sorchowski/odometry/schematics/DualEncoderI2C/dual-encoder-i2c-board-revf.png

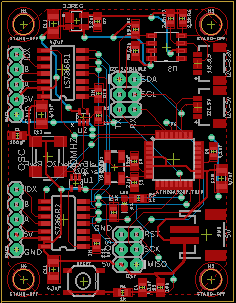
schematics/DualEncoderI2C/dual-encoder-i2c-board-revf.png
