sorchowski/odometry/schematics/DualEncoderShield3v/dual-encoder-shield-3v.jpg

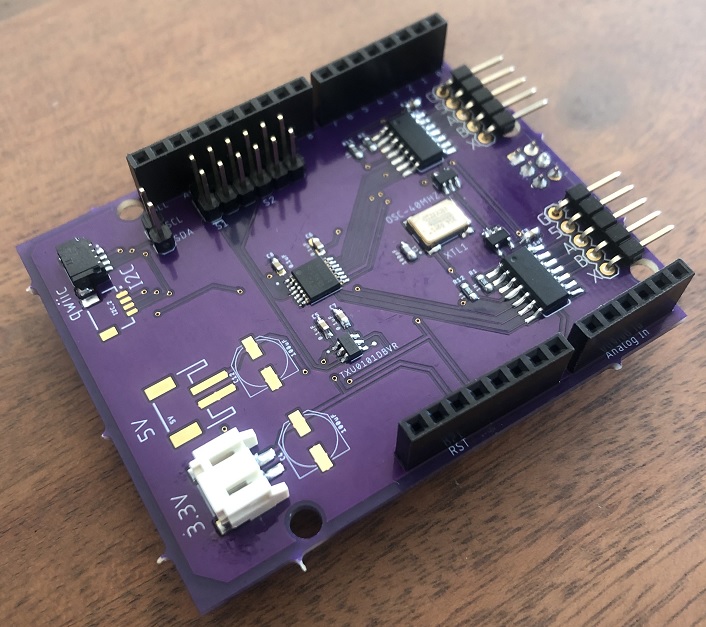
schematics/DualEncoderShield3v/dual-encoder-shield-3v.jpg
