sorchowski/odometry/schematics/DualEncoderShield5v/dual-encoder-shield-5v-revc-board.png

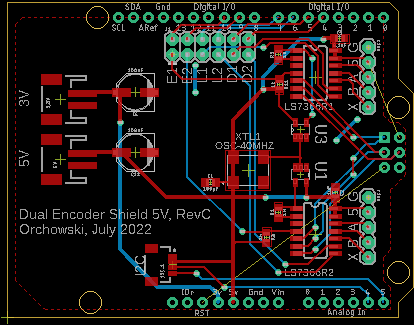
schematics/DualEncoderShield5v/dual-encoder-shield-5v-revc-board.png
